guajun/ELEC3300_FinalProject/SW/3300/OS.c

#include "OS.h"

#include "tim.h"

#include "stdint.h"

#include "DM4310.h"
#include "HT4310.h"
#include "GO_M8010_6.h"
#include "SpaceMouse.h"
#include "RotaryEncoder.h"
#include "IMU.h"
#include "Keyboard.h"

#define _2_M_PI      6.28318530717958647693  
#define M_PI		3.14159265358979323846
#define M_PI_2		1.57079632679489661923
#define M_PI_4		0.78539816339744830962
#define M_1_PI		0.31830988618379067154
#define M_2_PI		0.63661977236758134308


#define DM4310_POS_STEP 0.0004
#define HT4310_POS_STEP 10
#define GO_POS_STEP 0.0001

float OS_tickFreq = 0;

static void keyboardMotor()
{
    static float k;
    uint32_t encoder = RotaryEncoder_read();

    uint32_t num = encoder >> 2;

    if((int)encoder < 0)
    {
        num = 0;
    }
    else if(num > 15)
    {
        num = 15;
    }

    k = 1 + num * 0.25;

    if(keys.Q == KEY_STATE_PRESSED)
    {
        DM4310_insts[0].control.position += DM4310_POS_STEP * k;
    }
    else if(keys.A == KEY_STATE_PRESSED)
    {
        DM4310_insts[0].control.position -= DM4310_POS_STEP * k;
    }

    if(keys.W == KEY_STATE_PRESSED)
    {
        DM4310_insts[1].control.position += DM4310_POS_STEP * k;
    }
    else if(keys.S == KEY_STATE_PRESSED)
    {
        DM4310_insts[1].control.position -= DM4310_POS_STEP * k;
    }

    if(keys.E == KEY_STATE_PRESSED)
    {
        HT4310_insts[0].control.position += HT4310_POS_STEP * k;
    }
    else if(keys.D == KEY_STATE_PRESSED)
    {
        HT4310_insts[0].control.position -= HT4310_POS_STEP * k;
    }

    if(keys.R == KEY_STATE_PRESSED)
    {
        HT4310_insts[1].control.position += HT4310_POS_STEP * k;
    }
    else if(keys.F == KEY_STATE_PRESSED)
    {
        HT4310_insts[1].control.position -= HT4310_POS_STEP * k;
    }

    if(keys.T == KEY_STATE_PRESSED)
    {
        GO_M8010_6_insts[0].tarPos += GO_POS_STEP * k;
    }
    else if(keys.G == KEY_STATE_PRESSED)
    {
        GO_M8010_6_insts[0].tarPos -= GO_POS_STEP * k;
    }

    if(keys.Y == KEY_STATE_PRESSED)
    {
        GO_M8010_6_insts[1].tarPos += GO_POS_STEP * k;
    }
    else if(keys.H == KEY_STATE_PRESSED)
    {
        GO_M8010_6_insts[1].tarPos -= GO_POS_STEP * k;
    }
}

static void imuMotor()
{
    static float offsetYaw = 0.0f;
    static float offsetPitch = 0.0f;
    static float offsetRoll = 0.0f;

    offsetYaw = yaw - firstYaw;
    offsetPitch = pitch - firstPitch;
    offsetRoll =  roll - firstRoll;


    if(offsetYaw < -M_PI)
    {
        offsetYaw += _2_M_PI;
    }
    else if(offsetYaw > M_PI)
    {
        offsetYaw -= _2_M_PI;
    }

    if(offsetPitch < -M_PI)
    {
        offsetPitch += _2_M_PI;
    }
    else if(offsetPitch > M_PI)
    {
        offsetPitch -= _2_M_PI;
    }

    if(offsetRoll < -M_PI)
    {
        offsetRoll += _2_M_PI;
    }
    else if(offsetRoll > M_PI)
    {
        offsetRoll -= _2_M_PI;
    }

    // YAW QA
    DM4310_insts[0].control.position = firstYawMotor + offsetYaw;
    
    GO_M8010_6_insts[0].tarPos = firstPitchMotor + offsetPitch;

    HT4310_insts[0].control.position = (firstRollMotor + offsetRoll) * 81920;
}

static void spaceMouseMotor()
{
    DM4310_insts[0].control.position += (float)SpaceMouse_rxData.b / 16384 * 0.02f;
    DM4310_insts[1].control.position += (float)SpaceMouse_rxData.x / 16384 * 0.02f;

    HT4310_insts[0].control.position += (float)SpaceMouse_rxData.y / 16;
    HT4310_insts[1].control.position += (float)SpaceMouse_rxData.z / 16;

    GO_M8010_6_insts[0].tarPos += (float)SpaceMouse_rxData.a / 16384 * 0.03f;
    GO_M8010_6_insts[1].tarPos += (float)SpaceMouse_rxData.c / 16384 * 0.03f;
}

static void thread(TIM_HandleTypeDef *htim)
{
    static uint32_t lastTick = 0;
    OS_tickFreq = (HAL_GetTick() - lastTick) / 0.001;
    lastTick = HAL_GetTick();
    
    // static enum Key_State lastLKeyState = KEY_STATE_RELEASED;

    // if(lastLKeyState != keys.L && key)

    switch (motorCtr)
    {
    case 0:
        keyboardMotor();
        break;
    case 1:
        imuMotor();
        break;
    case 2:
        spaceMouseMotor();
    default:
        break;
    }

    

    DM4310_update();
    HT4310_update();
    GO_M8010_6_update();

}

void OS_init()
{
    HAL_TIM_RegisterCallback(&htim6, HAL_TIM_PERIOD_ELAPSED_CB_ID, thread);
    HAL_TIM_Base_Start_IT(&htim6);
}
